32teeth/SparkyJr/eagle/eagleUp/eagleUp_SparkySpecialK_board_bottom.jpg

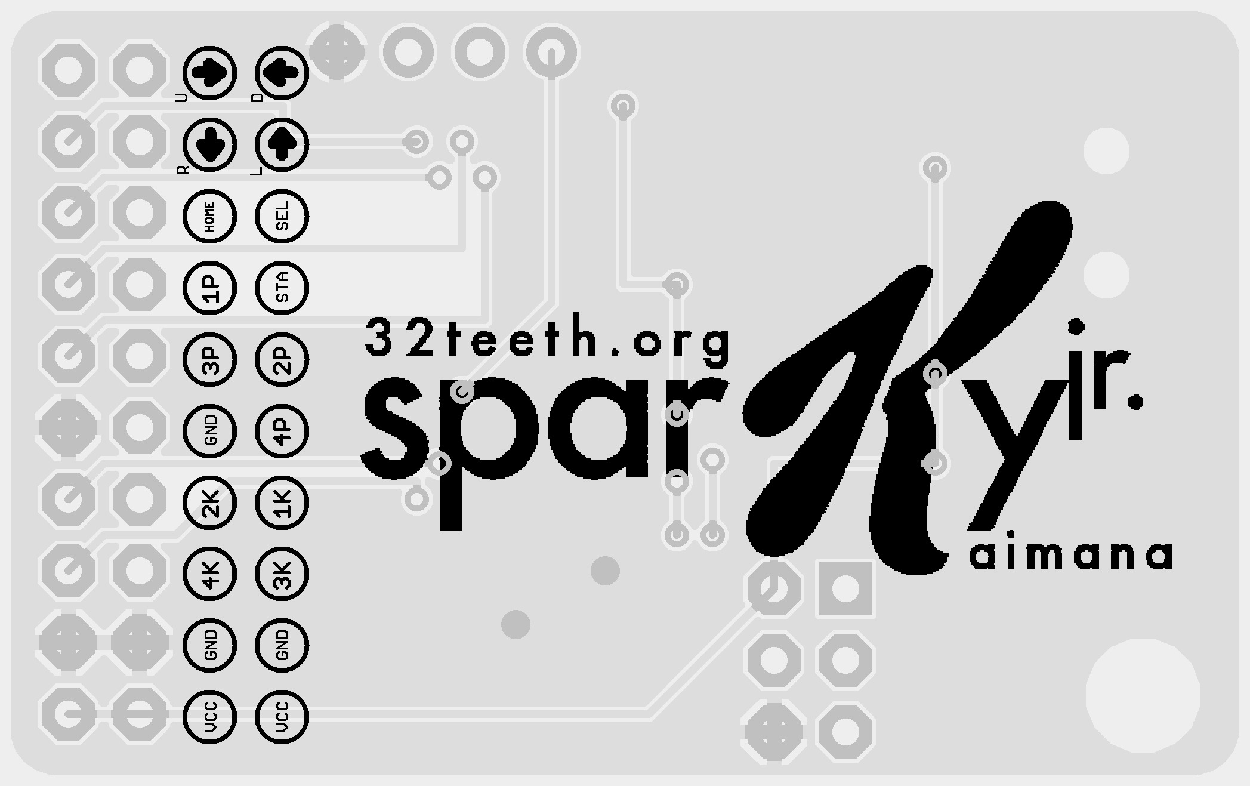
eagle/eagleUp/eagleUp_SparkySpecialK_board_bottom.jpg
