32teeth/SparkyJr/eagle/eagleUp/eagleUp_SparkySpecialK_board_bottom.png

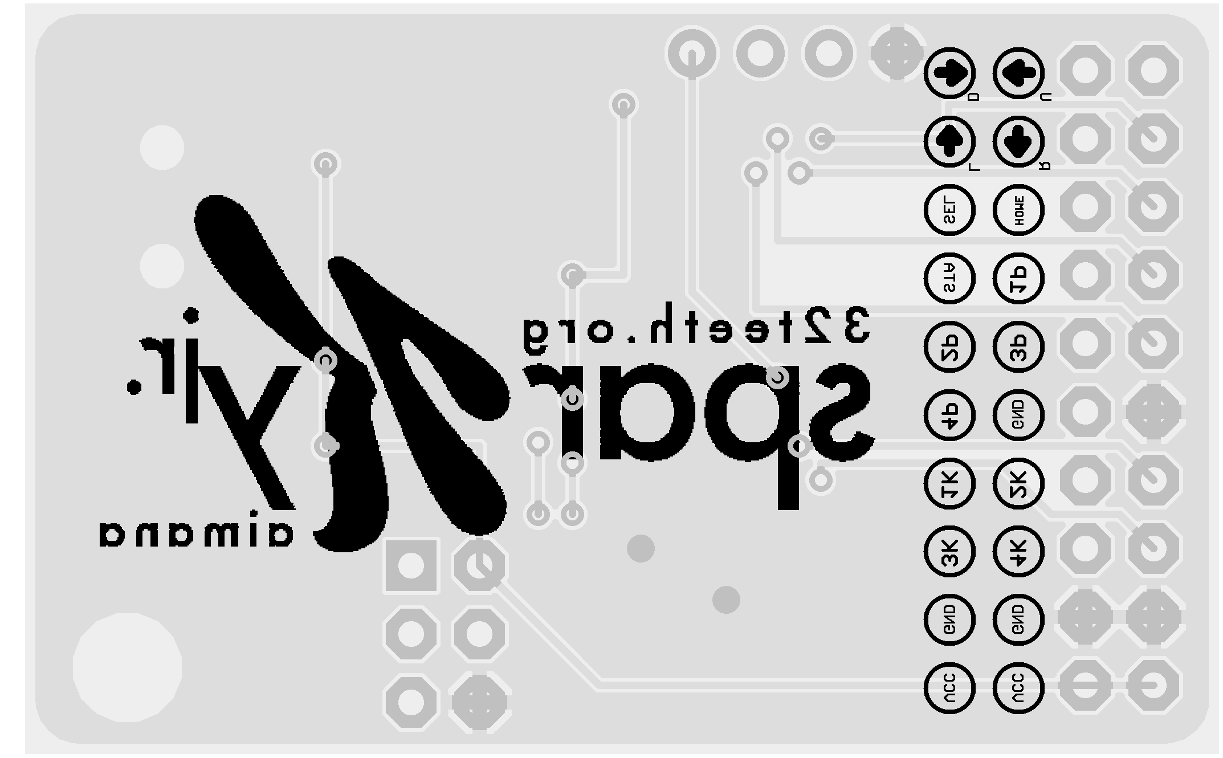
eagle/eagleUp/eagleUp_SparkySpecialK_board_bottom.png
