32teeth/SparkyJr/eagle/eagleUp/eagleUp_SparkySpecialK_bottom.png

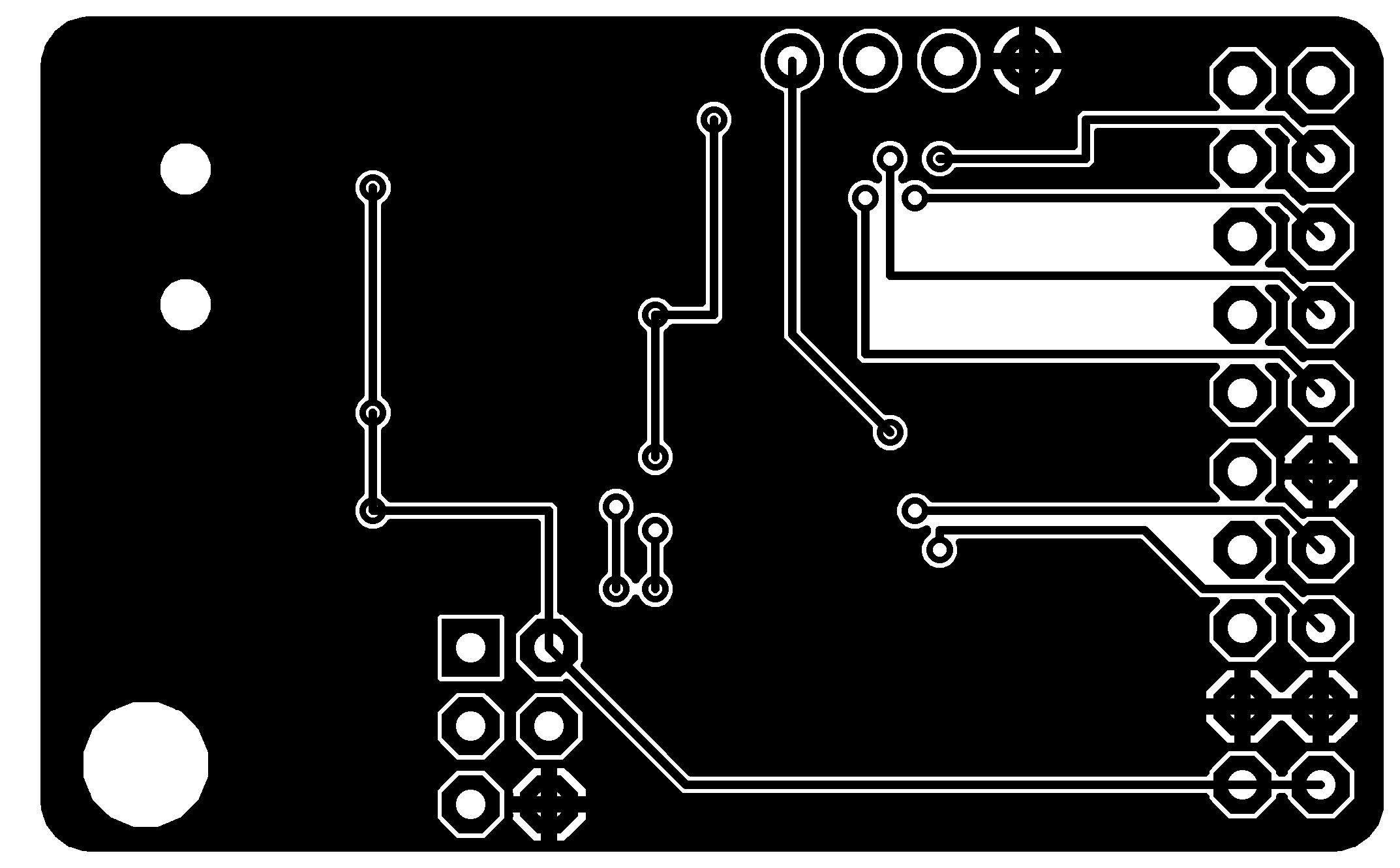
eagle/eagleUp/eagleUp_SparkySpecialK_bottom.png
