32teeth/SparkyJr/eagle/eagleUp/eagleUp_SparkySpecialK_bottom_mask.png

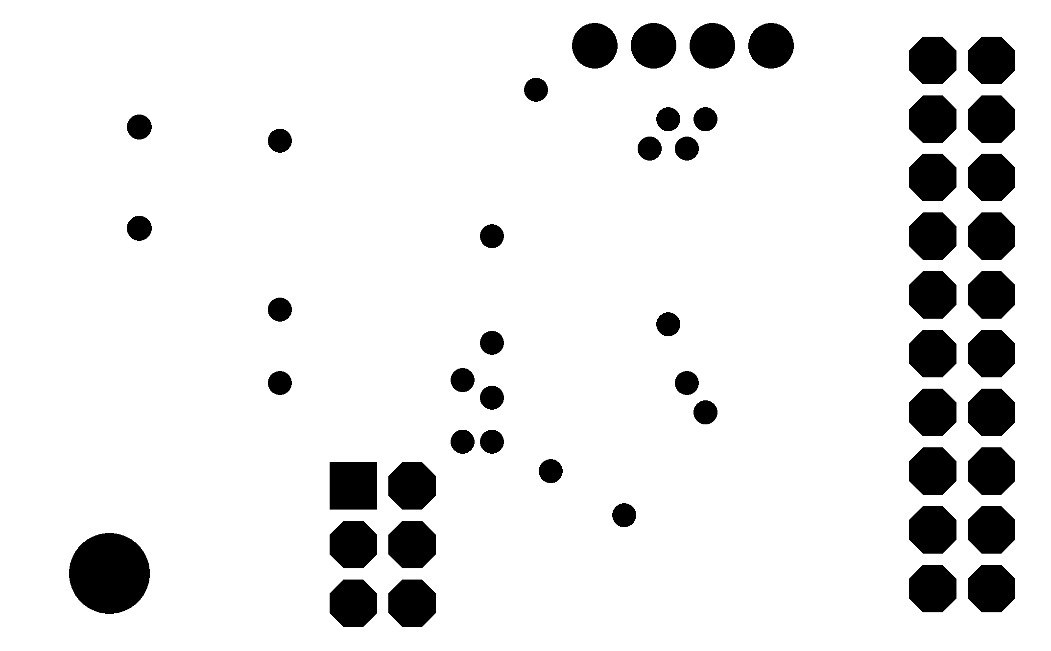
eagle/eagleUp/eagleUp_SparkySpecialK_bottom_mask.png
