32teeth/SparkyJr/eagle/eagleUp/eagleUp_SparkySpecialK_bottom_silk.png

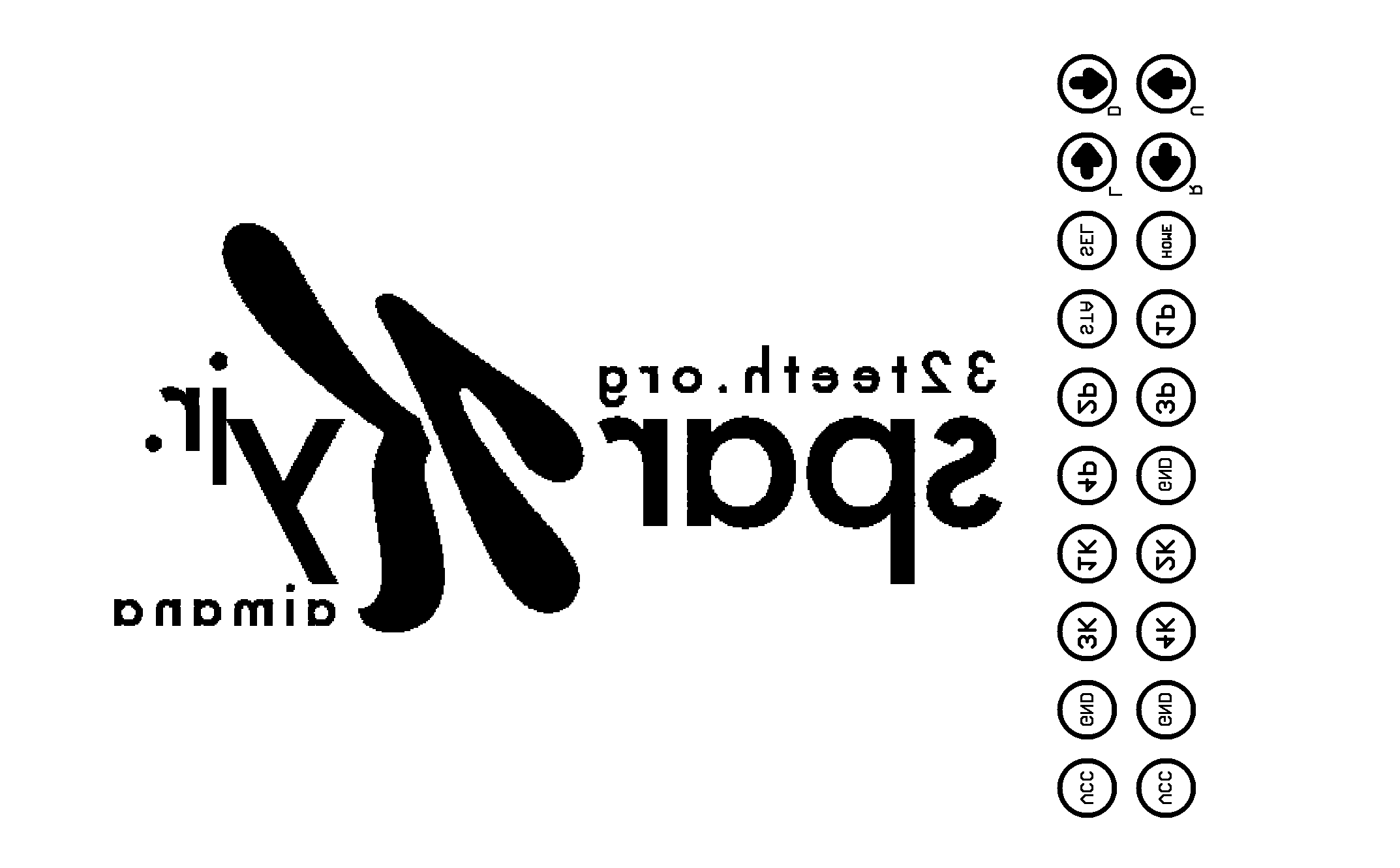
eagle/eagleUp/eagleUp_SparkySpecialK_bottom_silk.png
