32teeth/SparkyJr/eagle/eagleUp/eagleUp_SparkySpecialK_outline.png

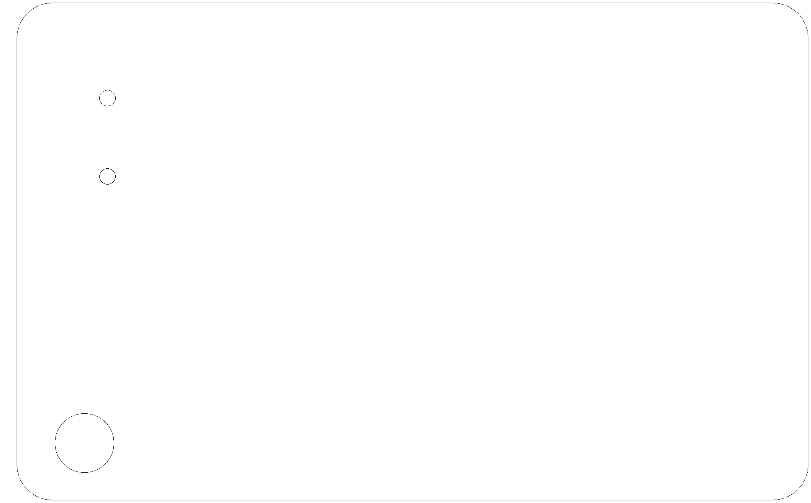
eagle/eagleUp/eagleUp_SparkySpecialK_outline.png
