32teeth/SparkyJr/eagle/eagleUp/eagleUp_SparkySpecialK_top_mask.png

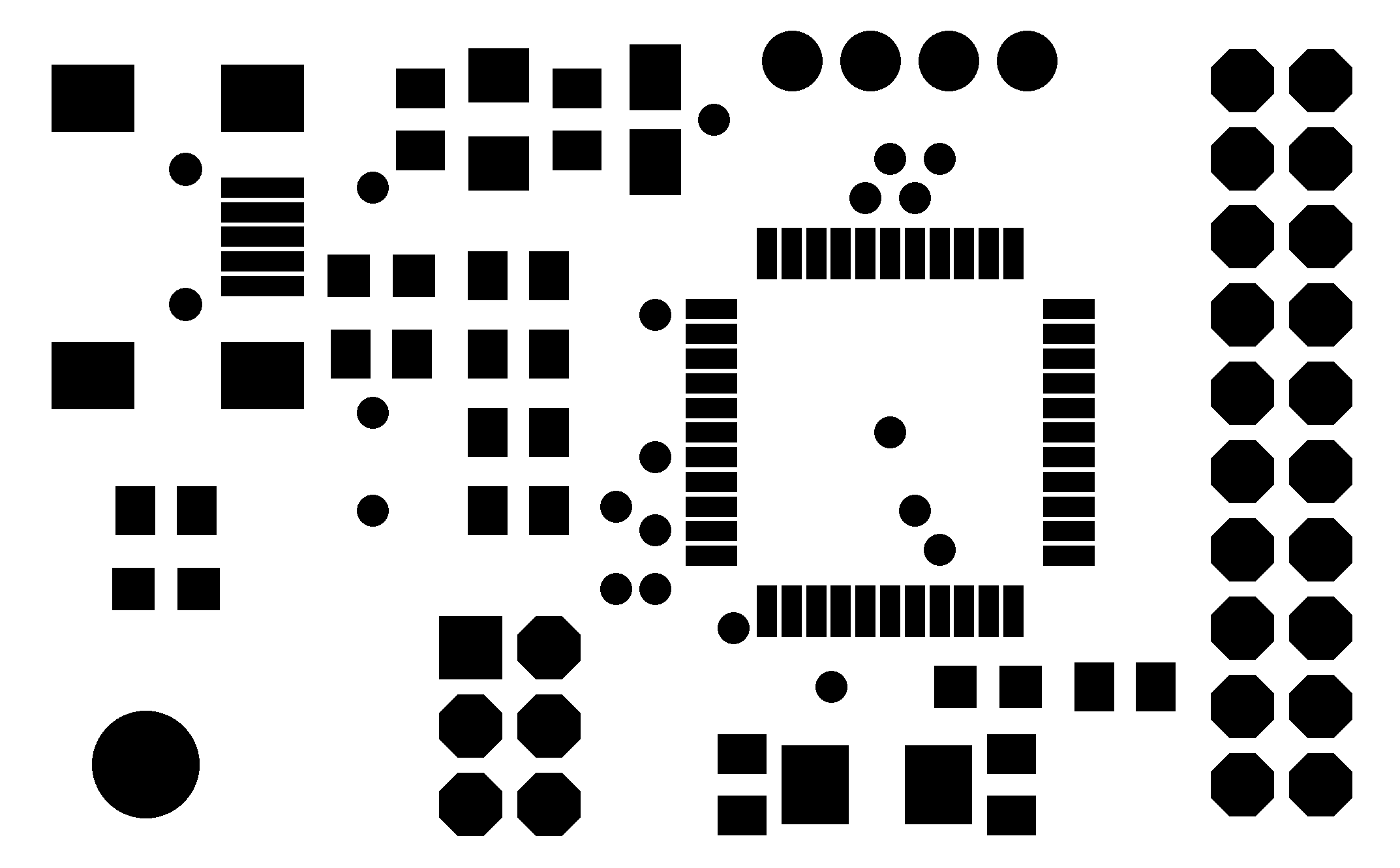
eagle/eagleUp/eagleUp_SparkySpecialK_top_mask.png
