32teeth/SparkyJr/eagle/eagleUp/eagleUp_SparkySpecialKExpansion_board_bottom.jpg

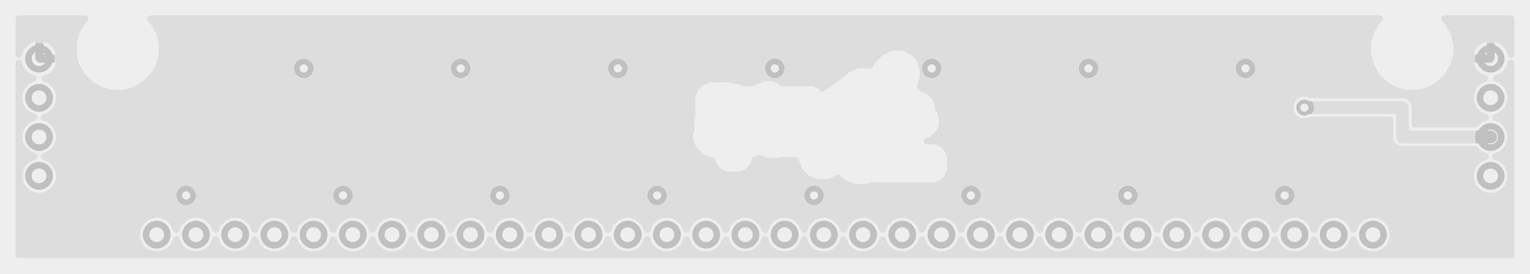
eagle/eagleUp/eagleUp_SparkySpecialKExpansion_board_bottom.jpg
