32teeth/SparkyJr/eagle/eagleUp/eagleUp_SparkySpecialKExpansion_board_bottom.png

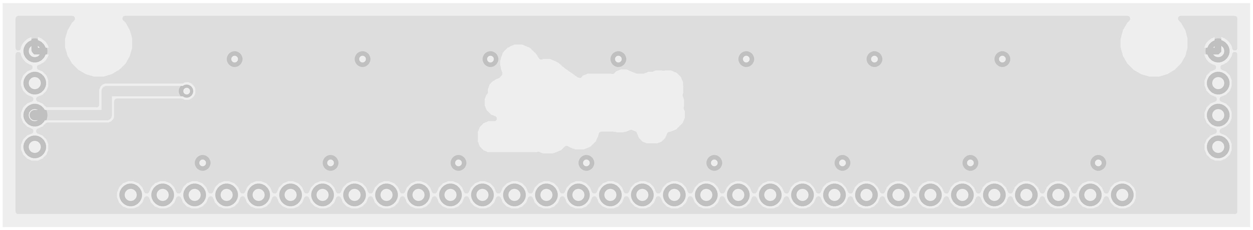
eagle/eagleUp/eagleUp_SparkySpecialKExpansion_board_bottom.png
