32teeth/SparkyJr/eagle/eagleUp/eagleUp_SparkySpecialKExpansion_board_top.jpg

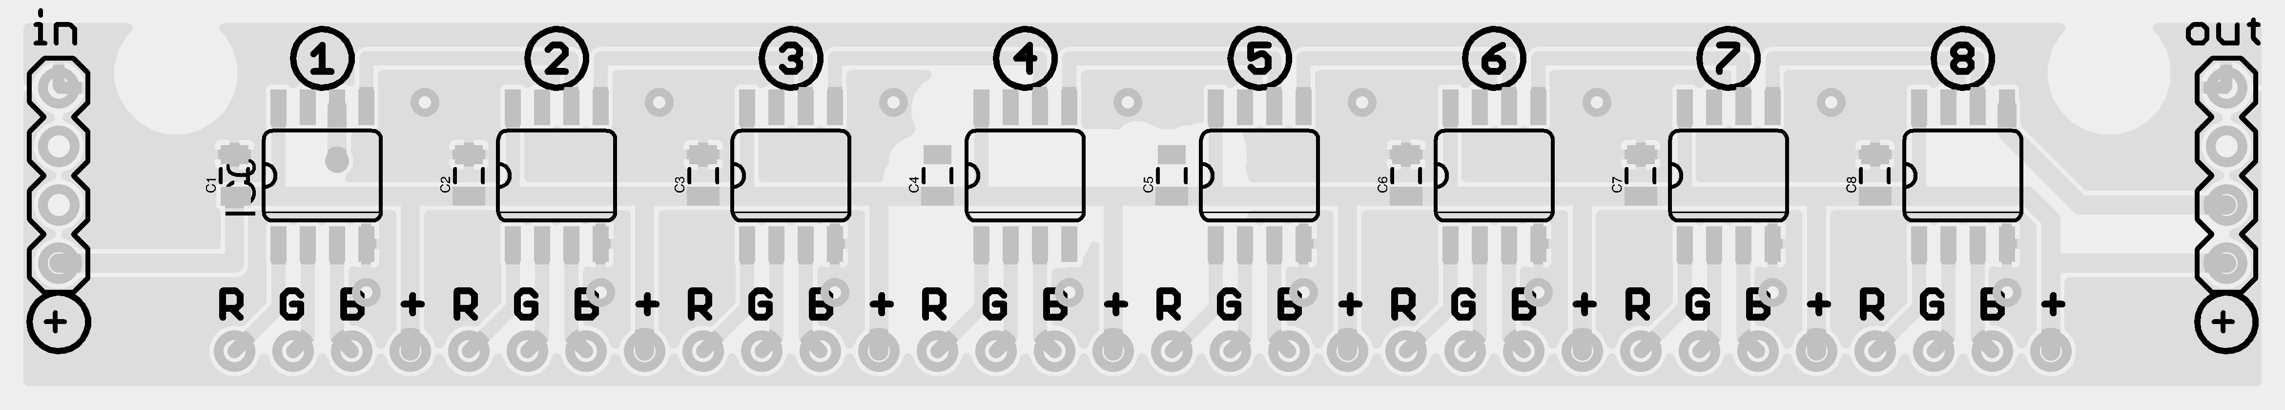
eagle/eagleUp/eagleUp_SparkySpecialKExpansion_board_top.jpg
