32teeth/SparkyJr/eagle/eagleUp/eagleUp_SparkySpecialKExpansion_board_top.png

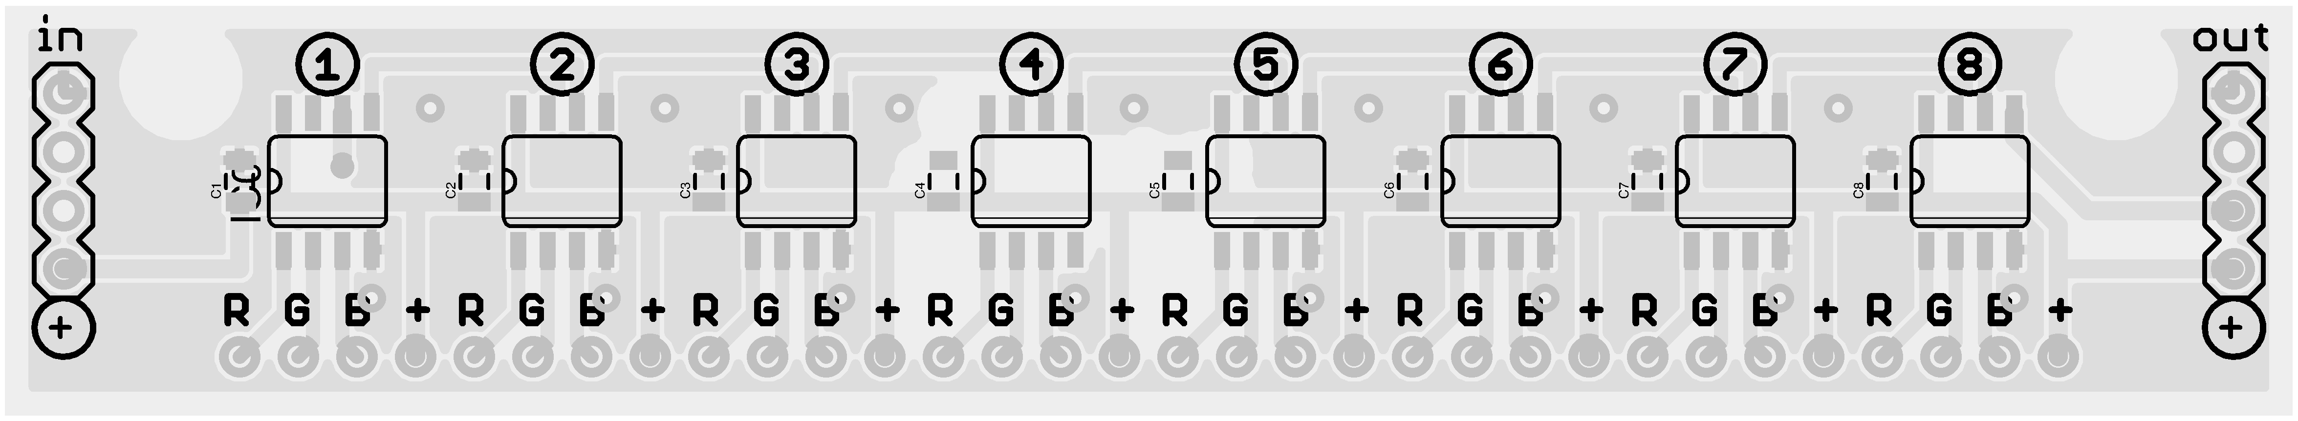
eagle/eagleUp/eagleUp_SparkySpecialKExpansion_board_top.png
