32teeth/SparkyJr/eagle/eagleUp/eagleUp_SparkySpecialKExpansion_bottom_mask.png

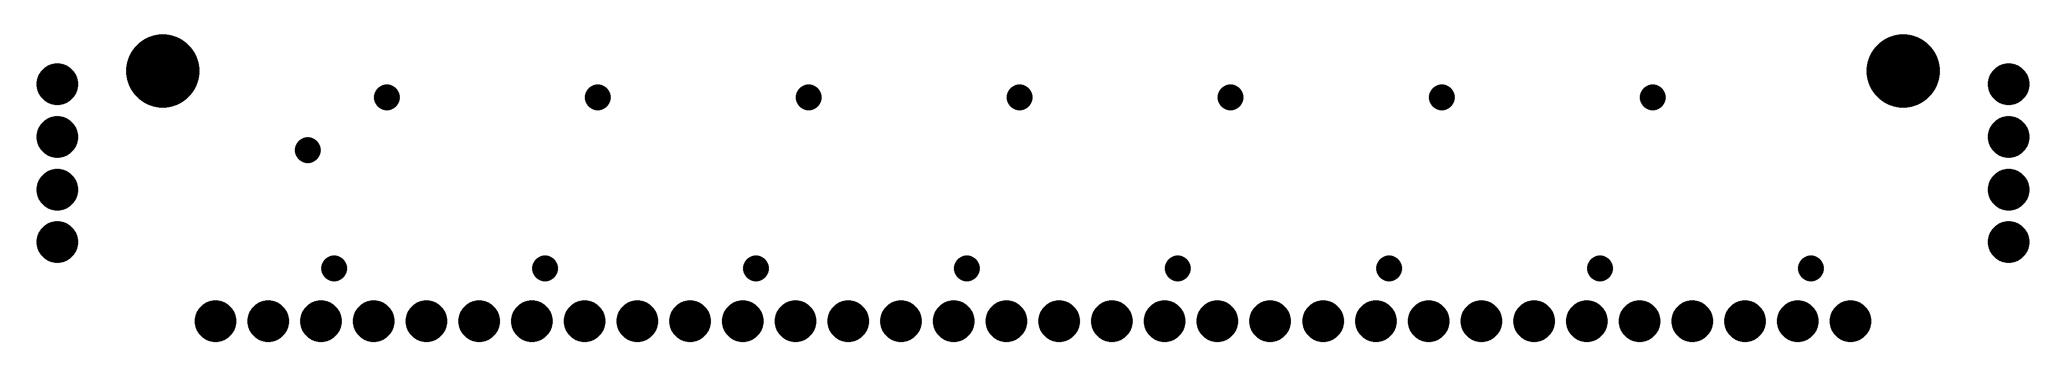
eagle/eagleUp/eagleUp_SparkySpecialKExpansion_bottom_mask.png
