32teeth/SparkyJr/eagle/eagleUp/eagleUp_SparkySpecialKExpansion_outline.png

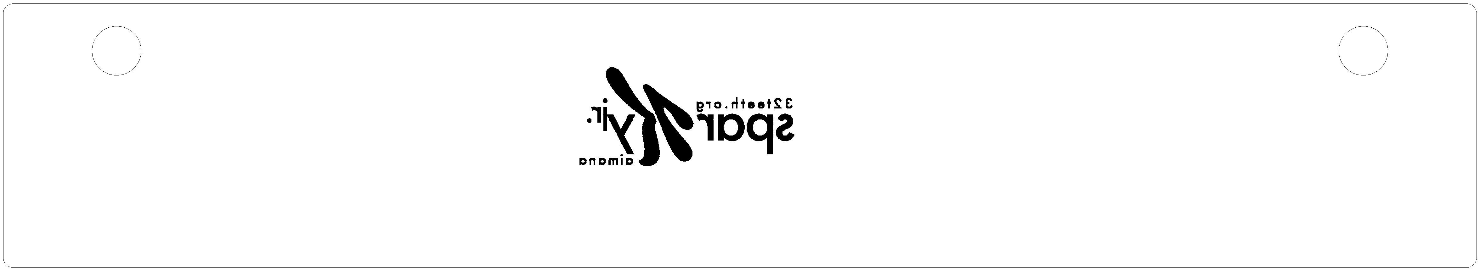
eagle/eagleUp/eagleUp_SparkySpecialKExpansion_outline.png
