32teeth/SparkyJr/eagle/eagleUp/eagleUp_SparkySpecialKExpansion_top.png

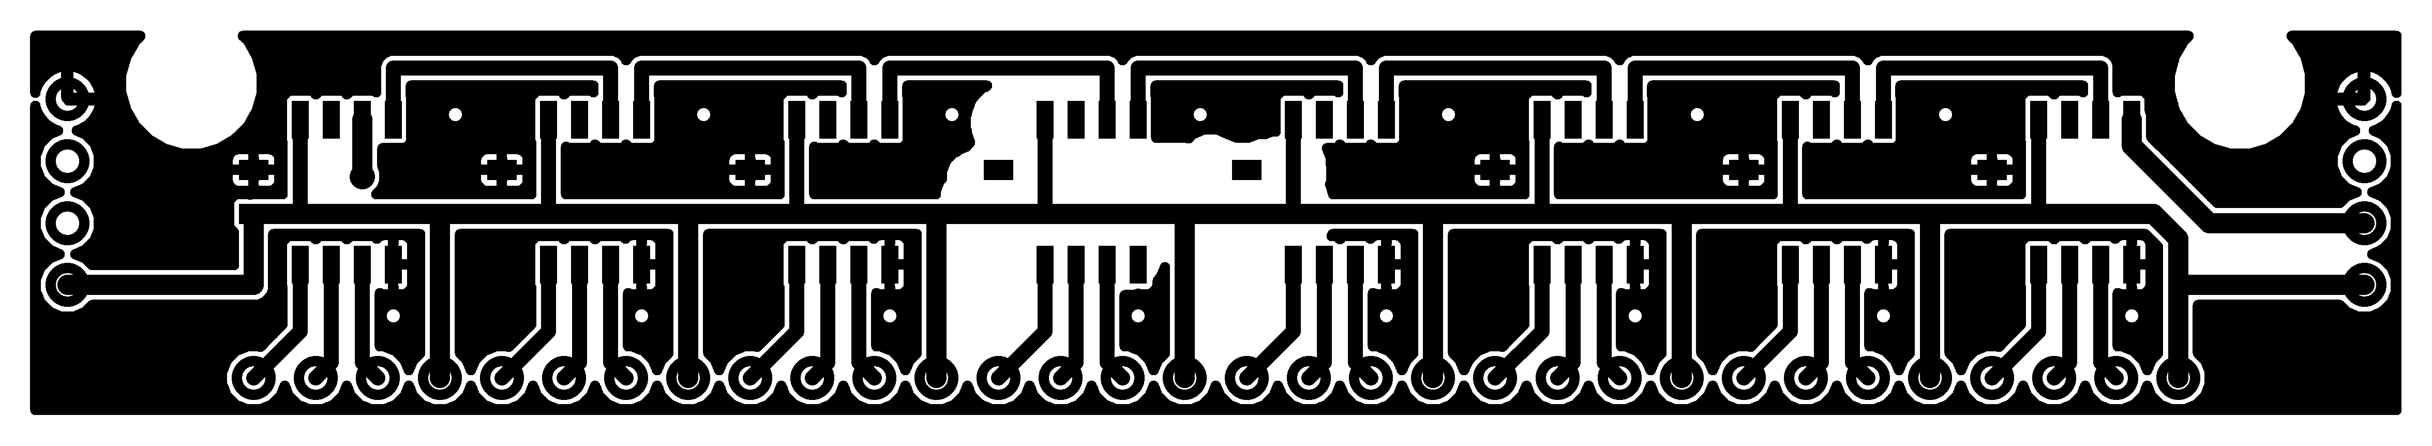
eagle/eagleUp/eagleUp_SparkySpecialKExpansion_top.png
