32teeth/SparkyJr/eagle/eagleUp/eagleUp_SparkySpecialKExpansion_top_mask.png

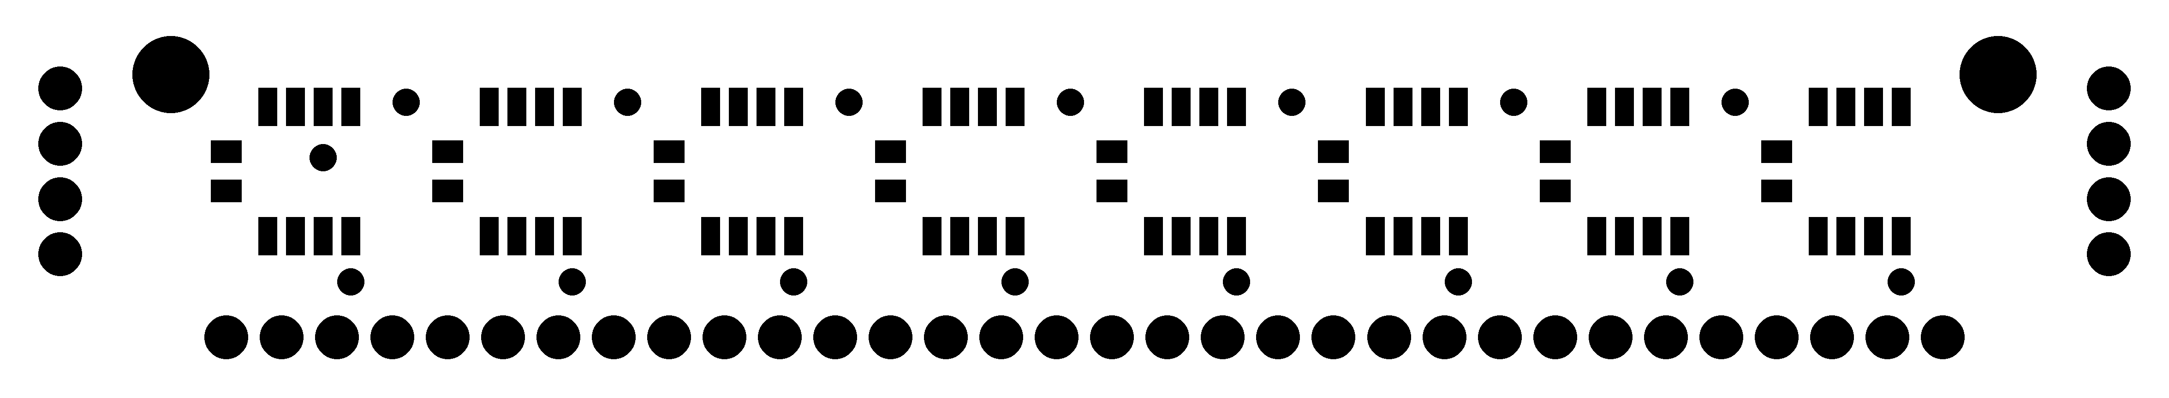
eagle/eagleUp/eagleUp_SparkySpecialKExpansion_top_mask.png
