32teeth/SparkyJr/google/v2/images/base.png

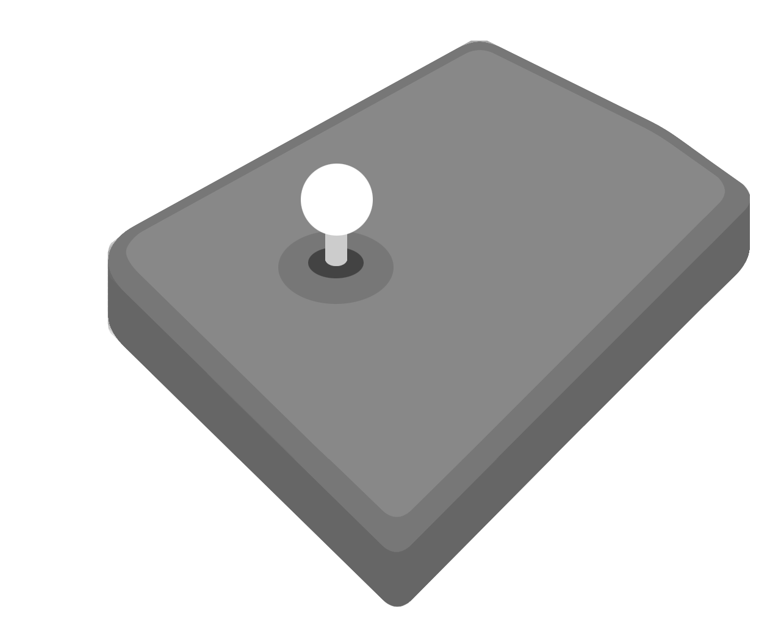
google/v2/images/base.png
