32teeth/SparkyJr/google/v2/images/colors.png

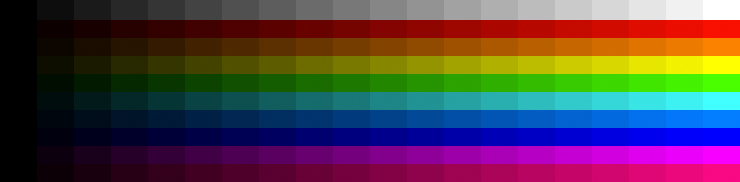
google/v2/images/colors.png
