32teeth/SparkyJr/google/v2/images/serial.png

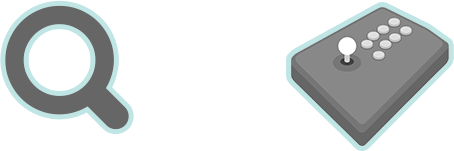
google/v2/images/serial.png
