32teeth/SparkyJr/google/v2/sparkyjr-128.png

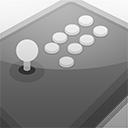
google/v2/sparkyjr-128.png
