32teeth/SparkyJr/images/http-::www.ebay.com:itm:181352046323_files/$_12.JPG

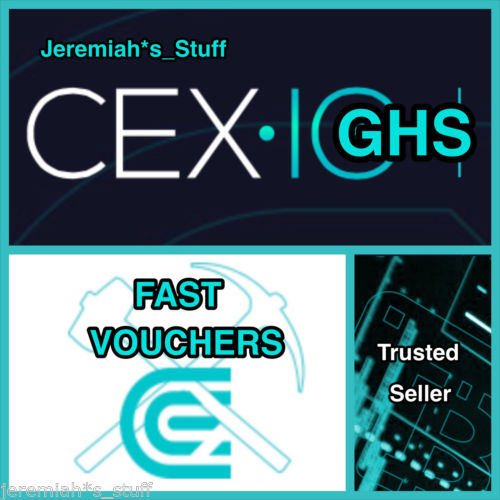
images/http-::www.ebay.com:itm:181352046323_files/$_12.JPG
