32teeth/SparkyJr/images/http-::www.ebay.com:itm:181352046323_files/BIN-Interrupt-Sample-Offer2.gif

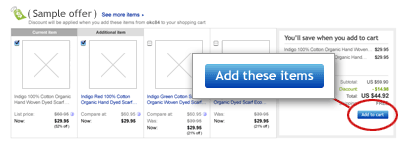
images/http-::www.ebay.com:itm:181352046323_files/BIN-Interrupt-Sample-Offer2.gif
