32teeth/SparkyJr/images/http-::www.ebay.com:itm:181352046323_files/spr14.png

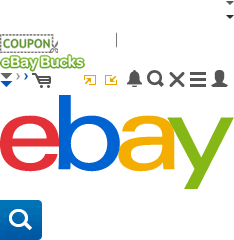
images/http-::www.ebay.com:itm:181352046323_files/spr14.png
