32teeth/SparkyJr/ios/SparkyJr/images/rainbow.png

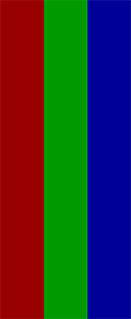
ios/SparkyJr/images/rainbow.png
