32teeth/SparkyJr/ios/SparkyJr/SparkyJr/images/stick.png

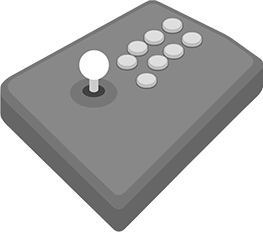
ios/SparkyJr/SparkyJr/images/stick.png
