32teeth/SparkyJr/processing/Sparky/data/blur.png

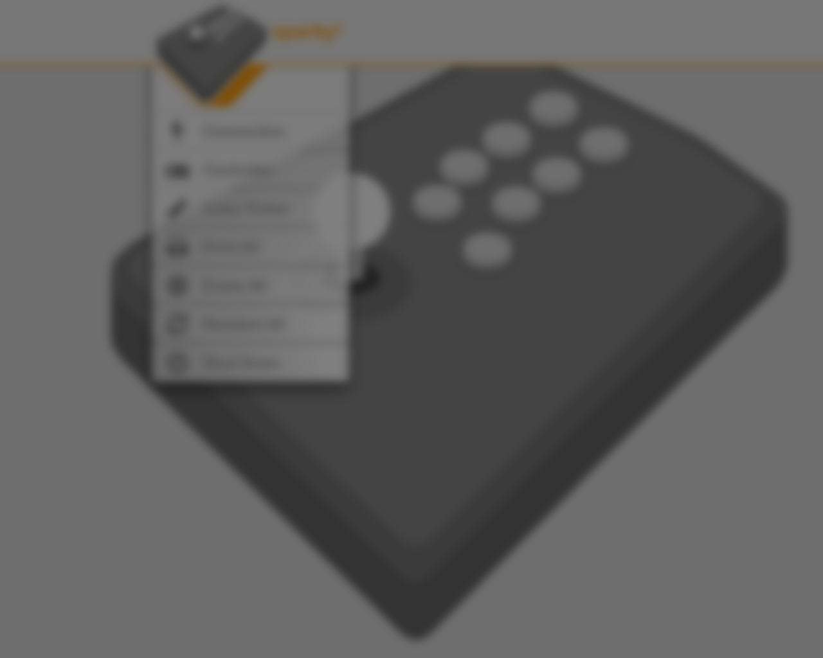
processing/Sparky/data/blur.png
