32teeth/SparkyJr/processing/Sparky/data/colorwheel.png

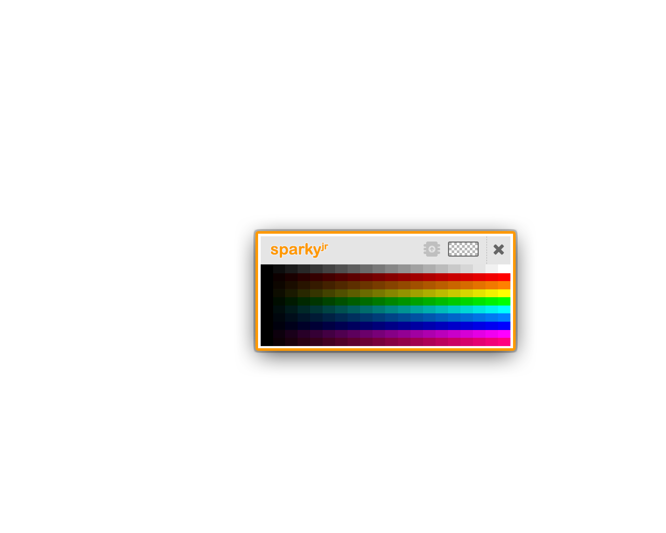
processing/Sparky/data/colorwheel.png
