32teeth/SparkyJr/processing/Sparky/data/header.png

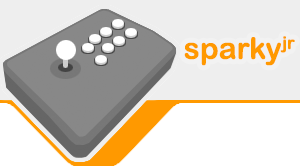
processing/Sparky/data/header.png
