32teeth/SparkyJr/processing/Sparky/data/loading.png

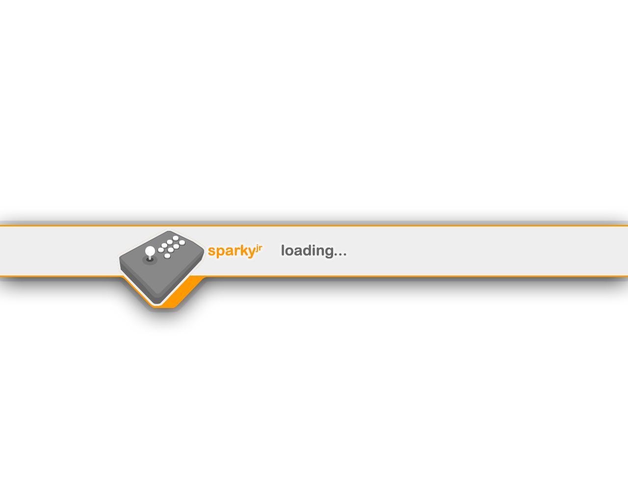
processing/Sparky/data/loading.png
