32teeth/SparkyJr/processing/Sparky/data/menu.png

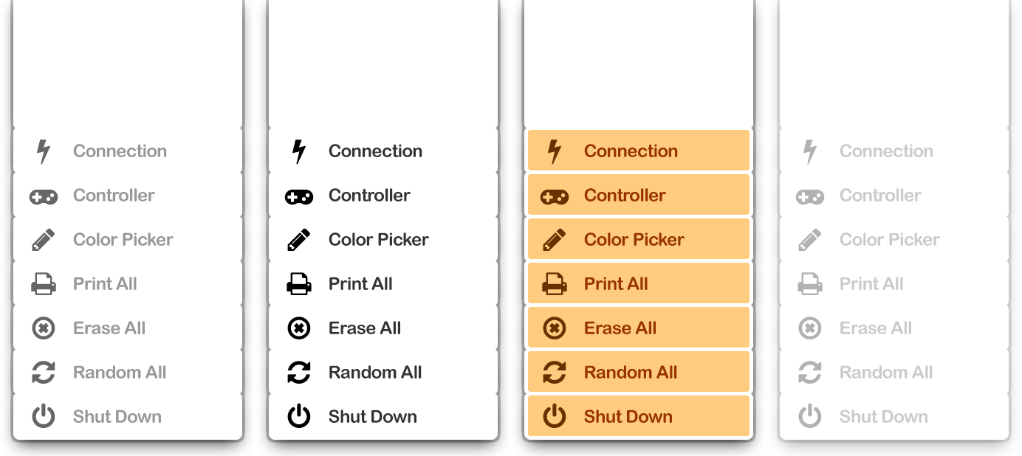
processing/Sparky/data/menu.png
