32teeth/SparkyJr/processing/Sparky/data/modal.png

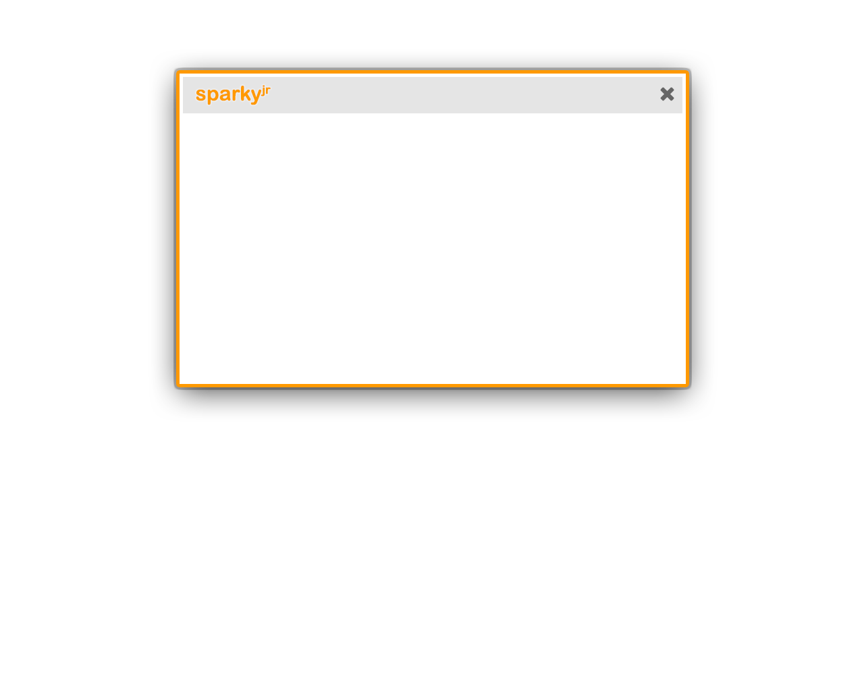
processing/Sparky/data/modal.png
