32teeth/SparkyJr/processing/Sparky/data/sketch.png

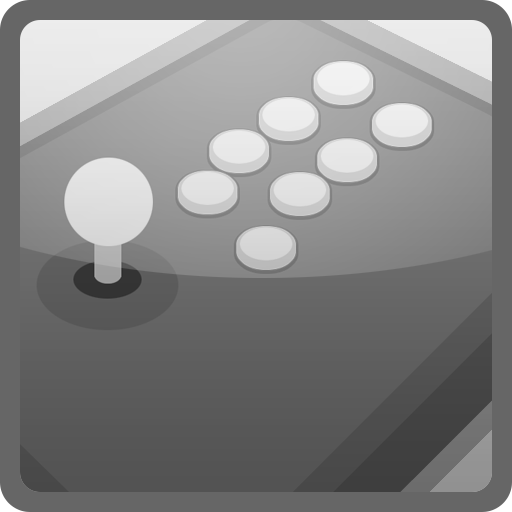
processing/Sparky/data/sketch.png
