32teeth/SparkyJr/processing/SparkyOfficial/SparkyOfficial/application.macosx/SparkyOfficial.app/Contents/Resources/Java/data/color-picker-upload.png

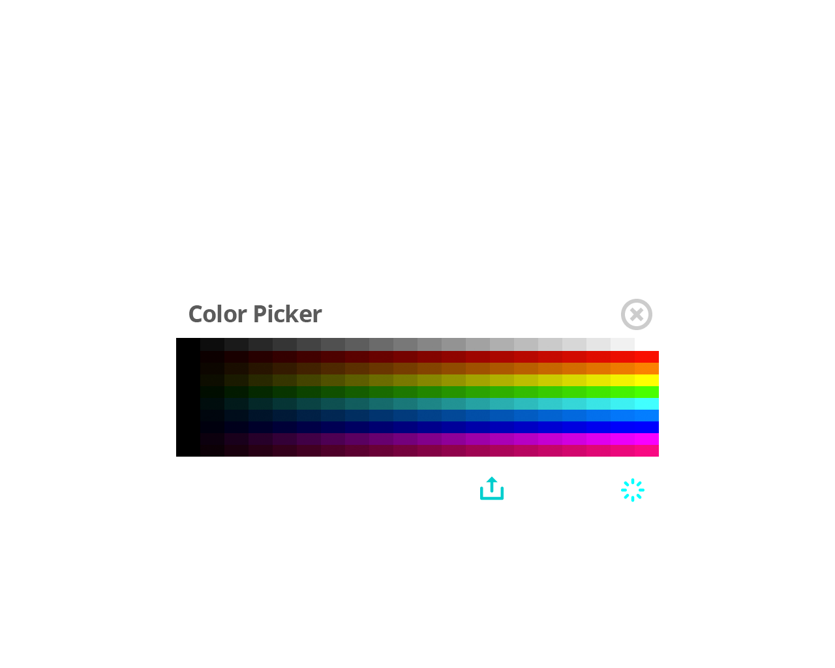
processing/SparkyOfficial/SparkyOfficial/application.macosx/SparkyOfficial.app/Contents/Resources/Java/data/color-picker-upload.png
