32teeth/SparkyJr/processing/SparkyOfficial/SparkyOfficial/application.macosx/SparkyOfficial.app/Contents/Resources/Java/data/device-connection-hover.png

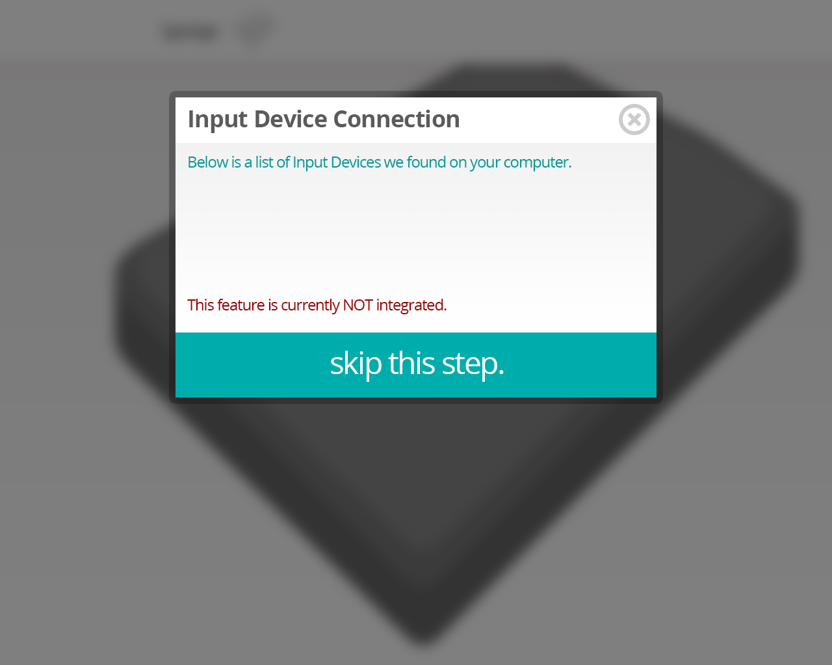
processing/SparkyOfficial/SparkyOfficial/application.macosx/SparkyOfficial.app/Contents/Resources/Java/data/device-connection-hover.png
