32teeth/SparkyJr/processing/SparkyOfficial/SparkyOfficial/application.macosx/SparkyOfficial.app/Contents/Resources/Java/data/device-hover.png

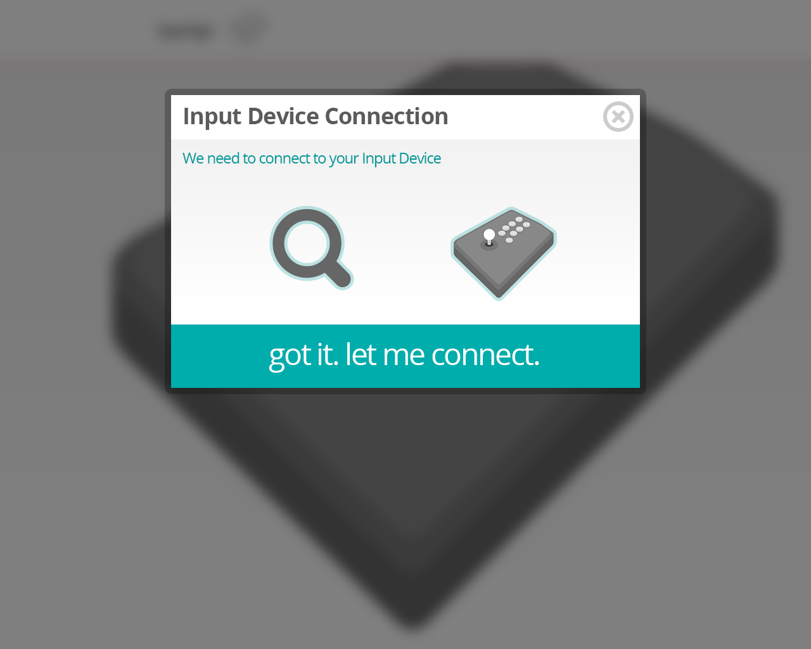
processing/SparkyOfficial/SparkyOfficial/application.macosx/SparkyOfficial.app/Contents/Resources/Java/data/device-hover.png
