32teeth/SparkyJr/processing/SparkyOfficial/SparkyOfficial/application.macosx/SparkyOfficial.app/Contents/Resources/Java/data/intro-rainbow.png

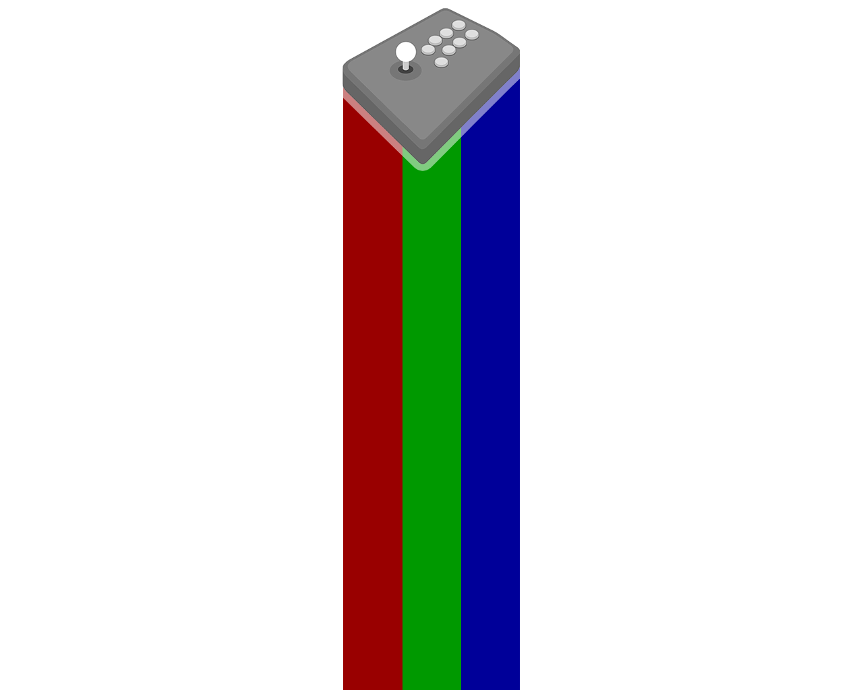
processing/SparkyOfficial/SparkyOfficial/application.macosx/SparkyOfficial.app/Contents/Resources/Java/data/intro-rainbow.png
