32teeth/SparkyJr/www/images/doge.png

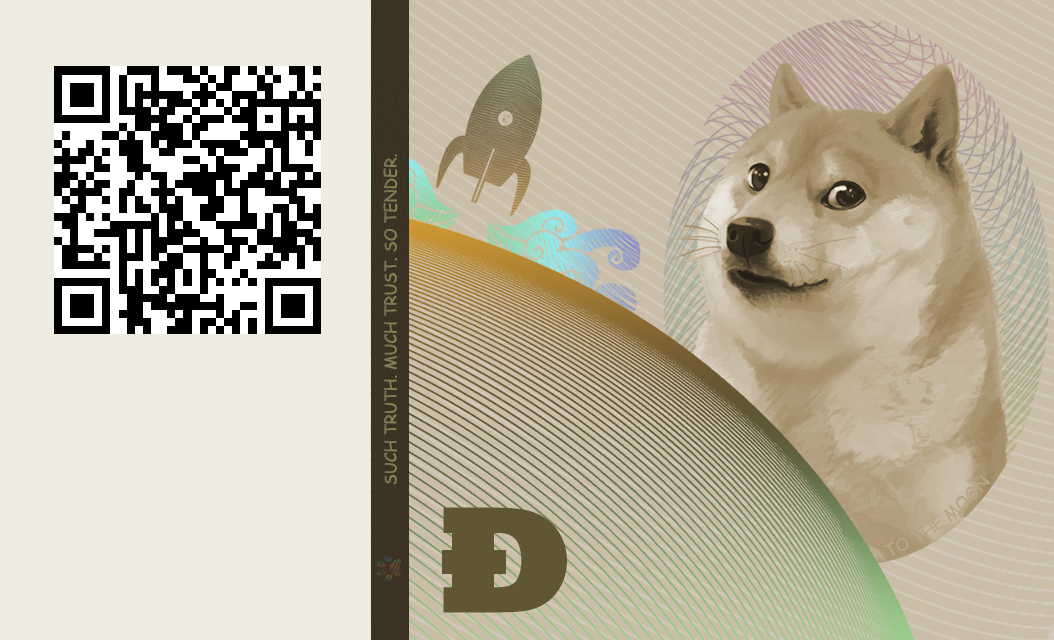
www/images/doge.png
