32teeth/SparkyJr/www/video/hero.png

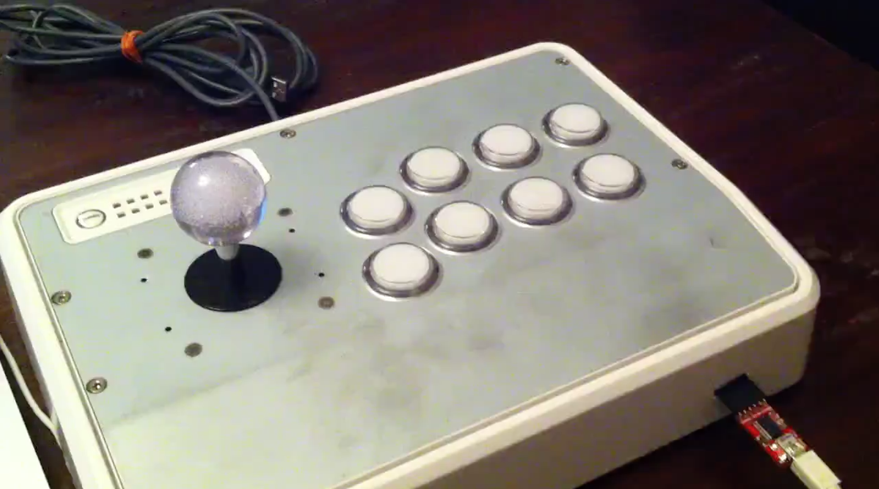
www/video/hero.png
