32teeth/SparkyJr/www/video/sparkydark.jpg

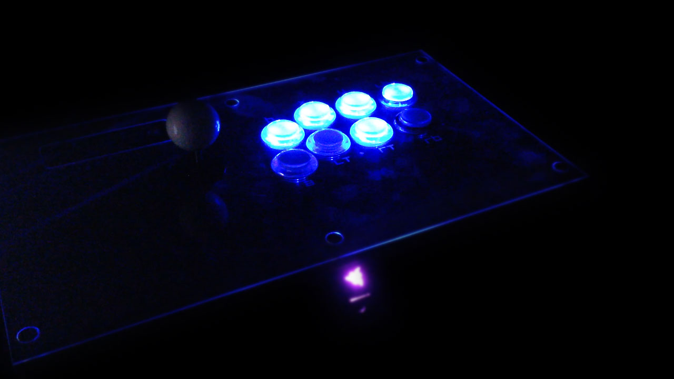
www/video/sparkydark.jpg
