32teeth/SparkyJr/www/video/teaser.jpg

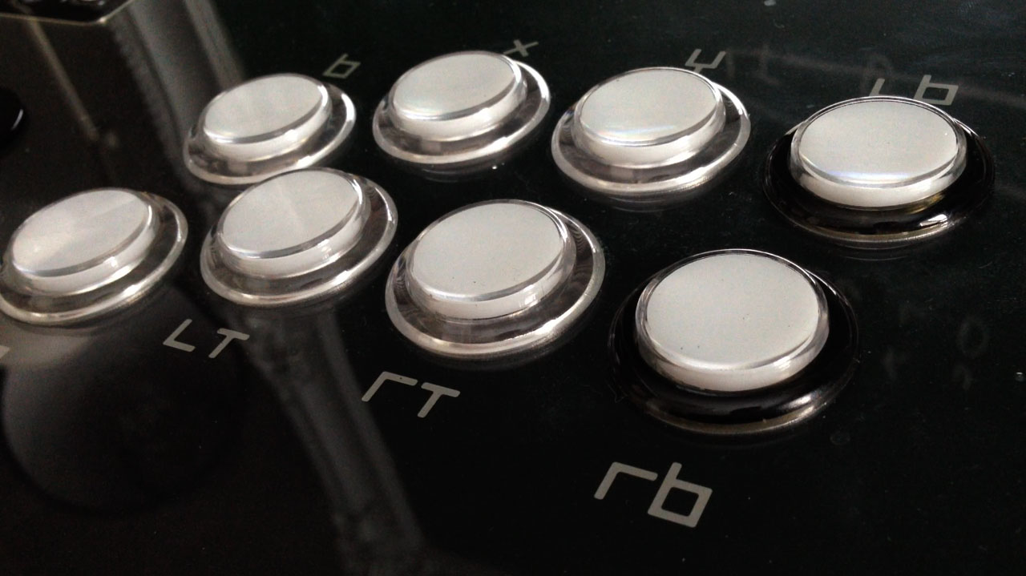
www/video/teaser.jpg
