32teeth/SparkyJr/arduino/Sparky/colors.h

/*
** @desc List of color constants converted into 565 from RGB
*/  
#define MAROON getLong(128,0,0)
#define RED getLong(255,0,0)
#define TOMATO getLong(255,99,71)
#define CORAL getLong(255,127,80)
#define INDIAN_RED getLong(205,92,92)
#define LIGHT_CORAL getLong(240,128,128)
#define DARK_SALMON getLong(233,150,122)
#define SALMON getLong(250,128,114)
#define LIGHT_SALMON getLong(255,160,122)
#define ORANGE_RED getLong(255,69,0)
#define DARK_ORANGE getLong(255,140,0)
#define ORANGE getLong(255,165,0)
#define GOLD getLong(255,215,0)
#define DARK_GOLDEN_ROD getLong(184,134,11)
#define GOLDEN_ROD getLong(218,165,32)
#define PALE_GOLDEN_ROD getLong(238,232,170)
#define DARK_KHAKI getLong(189,183,107)
#define KHAKI getLong(240,230,140)
#define OLIVE getLong(128,128,0)
#define YELLOW getLong(255,255,0)
#define YELLOW_GREEN getLong(154,205,50)
#define DARK_OLIVE_GREEN getLong(85,107,47)
#define OLIVE_DRAB getLong(107,142,35)
#define LAWN_GREEN getLong(124,252,0)
#define CHART_REUSE getLong(127,255,0)
#define GREEN_YELLOW getLong(173,255,47)
#define DARK_GREEN getLong(0,100,0)
#define GREEN getLong(0,128,0)
#define FOREST_GREEN getLong(34,139,34)
#define LIME getLong(0,255,0)
#define LIME_GREEN getLong(50,205,50)
#define LIGHT_GREEN getLong(144,238,144
#define PALE_GREEN getLong(152,251,152)
#define DARK_SEA_GREEN getLong(143,188,143)
#define MEDIUM_SPRING_GREEN getLong(0,250,154)
#define SPRING_GREEN getLong(0,255,127)
#define SEA_GREEN getLong(46,139,87)
#define MEDIUM_AQUA_MARINE getLong(102,205,170)
#define MEDIUM_SEA_GREEN getLong(60,179,113)
#define LIGHT_SEA_GREEN getLong(32,178,170)
#define DARK_SLATE_GRAY getLong(47,79,79)
#define TEAL getLong(0,128,128)
#define DARK_CYAN getLong(0,139,139)
#define AQUA getLong(0,255,255)
#define CYAN getLong(0,255,255)
#define LIGHT_CYAN getLong(224,255,255)
#define DARK_TURQUOISE getLong(0,206,209)
#define TURQUOISE getLong(64,224,208)
#define MEDIUM_TURQUOISE getLong(72,209,204)
#define PALE_TURQUOISE getLong(175,238,238)
#define AQUA_MARINE getLong(127,255,212)
#define POWDER_BLUE getLong(176,224,230)
#define CADET_BLUE getLong(95,158,160)
#define STEEL_BLUE getLong(70,130,180)
#define CORN_FLOWER_BLUE getLong(100,149,237)
#define DEEP_SKY_BLUE getLong(0,191,255)
#define DODGER_BLUE getLong(30,144,255)
#define LIGHT_BLUE getLong(173,216,230)
#define SKY_BLUE getLong(135,206,235)
#define LIGHT_SKY_BLUE getLong(135,206,250)
#define MIDNIGHT_BLUE getLong(25,25,112)
#define NAVY getLong(0,0,128)
#define DARK_BLUE getLong(0,0,139)
#define MEDIUM_BLUE getLong(0,0,205)
#define BLUE getLong(0,0,255)
#define ROYAL_BLUE getLong(65,105,225)
#define BLUE_VIOLET getLong(138,43,226)
#define INDIGO getLong(75,0,130)
#define DARK_SLATE_BLUE getLong(72,61,139)
#define SLATE_BLUE getLong(106,90,205)
#define MEDIUM_SLATE_BLUE getLong(123,104,238)
#define MEDIUM_PURPLE getLong(147,112,219)
#define DARK_MAGENTA getLong(139,0,139)
#define DARK_VIOLET getLong(148,0,211)
#define DARK_ORCHID getLong(153,50,204)
#define MEDIUM_ORCHID getLong(186,85,211)
#define PURPLE getLong(128,0,128)
#define THISTLE getLong(216,191,216)
#define PLUM getLong(221,160,221)
#define VIOLET getLong(238,130,238)
#define MAGENTA getLong(255,0,255)
#define ORCHID getLong(218,112,214)
#define MEDIUM_VIOLET_RED getLong(199,21,133)
#define PALE_VIOLET_RED getLong(219,112,147)
#define DEEP_PINK getLong(255,20,147)
#define HOT_PINK getLong(255,105,180)
#define LIGHT_PINK getLong(255,182,193)
#define PINK getLong(255,192,203)
#define ANTIQUE_WHITE getLong(250,235,215)
#define BEIGE getLong(245,245,220)
#define BISQUE getLong(255,228,196)
#define BLANCHED_ALMOND getLong(255,235,205)
#define WHEAT getLong(245,222,179)
#define CORN_SILK getLong(255,248,220)
#define LEMON_CHIFFON getLong(255,250,205)
#define LIGHT_GOLDEN_ROD_YELLOW getLong(250,250,210)
#define LIGHT_YELLOW getLong(255,255,224)
#define SADDLE_BROWN getLong(139,69,19)
#define SIENNA getLong(160,82,45)
#define CHOCOLATE getLong(210,105,30)
#define PERU getLong(205,133,63)
#define SANDY_BROWN getLong(244,164,96)
#define BURLY_WOOD getLong(222,184,135)
#define TAN getLong(210,180,140)
#define ROSY_BROWN getLong(188,143,143)
#define MOCCASIN getLong(255,228,181)
#define NAVAJO_WHITE getLong(255,222,173)
#define PEACH_PUFF getLong(255,218,185)
#define MISTY_ROSE getLong(255,228,225)
#define LAVENDER_BLUSH getLong(255,240,245)
#define LINEN getLong(250,240,230)
#define OLD_LACE getLong(253,245,230)
#define PAPAYA_WHIP getLong(255,239,213)
#define SEA_SHELL getLong(255,245,238)
#define MINT_CREAM getLong(245,255,250)
#define SLATE_GRAY getLong(112,128,144)
#define LIGHT_SLATE_GRAY getLong(119,136,153)
#define LIGHT_STEEL_BLUE getLong(176,196,222)
#define LAVENDER getLong(230,230,250)
#define FLORAL_WHITE getLong(255,250,240)
#define ALICE_BLUE getLong(240,248,255)
#define GHOST_WHITE getLong(248,248,255)
#define HONEYDEW getLong(240,255,240)
#define IVORY getLong(255,255,240)
#define AZURE getLong(240,255,255)
#define SNOW getLong(255,250,250)
#define BLACK getLong(0,0,0)
#define DIM_GRAY getLong(105,105,105)
#define GRAY getLong(128,128,128)
#define DARK_GRAY  getLong(169,169,169)
#define SILVER getLong(192,192,192)
#define LIGHT_GRAY  getLong(211,211,211)
#define GAINSBORO getLong(220,220,220)
#define WHITE_SMOKE getLong(245,245,245)
#define WHITE getLong(255,255,255)


/*
** @desc assign color values
*/
long int color;
long int colors[14] = {RED, ORANGE, YELLOW, GREEN, LIME, TEAL, AQUA, TURQUOISE, NAVY, BLUE, INDIGO, PURPLE, PINK, WHITE};
