32teeth/SparkyJr/arduino/Sparky/eeprom.h

int block;

/*
** @method setEEPROM
** @param address {int} 0-254
** @param color {long}
** @desc set eeprom address with color
*/
void setEEPROM(int address, long color)
{
  block = address*4;
  EEPROM.writeLong(block, color);
}

/*
** @method getColorEEPROM
** @param address {int} 0-254
** @desc get color from eeprom address
*/
int* getColorEEPROM(int address)
{
  block = address*4;
  long color = EEPROM.readLong(block);
  return getRGB(color);
}

/*
** @method getLongEEPROM
** @param address {int} 0-254
** @desc get color from eeprom address
*/
long getLongEEPROM(int address)
{
  block = address*4;
  return EEPROM.readLong(block);
}

/*
** @method randomEEPROM
** @desc assign random colors to address
*/
void randomEEPROM()
{
  for(int n = 0; n < addressMax; n+=4)
  {
    EEPROM.writeLong(n, colors[random(0,13)]);
    delay(10);
  }  
}

/*
** @method printEEPROM
** @desc print out all EEPROM address
*/
void printEEPROM()
{
  for(int n = 0; n < addressMax; n+=4)
  {
    Serial.print("reading address:");
    Serial.print(n/4);
    Serial.print("\tlong:");
    Serial.println(EEPROM.readLong(n));
  }  
}

/*
** @method eraseEEPROM
** @desc print out all EEPROM address
*/
void eraseEEPROM()
{
  for(int n = 0; n < addressMax; n+=4)
  {
    EEPROM.writeLong(n, empty);
    delay(10);
  }  
}
